Iknowalittle/A-magnetic-loop-antenna-tuner/MovingAverage.ino

#include "MovingAverage.h"

MovingAverageFilter::MovingAverageFilter(unsigned int newDataPointsCount)
{
  k = 0; //initialize so that we start to write at index 0
  if (newDataPointsCount < MAX_DATA_POINTS)
    dataPointsCount = newDataPointsCount;
  else
    dataPointsCount = MAX_DATA_POINTS;

  for (i = 0; i < dataPointsCount; i++)
  {
    values[i] = 0; // fill the array with 0's
  }
}

float MovingAverageFilter::process(float in)
{
  out = 0;

  if (k>dataPointsCount) k=0;

  values[k] = in;
  k++;

  for (i = 0; i < k; i++)
  {
     out += values[i];
  }

  return out / k;
}
